aeonSolutions/AeonLabs-Solder-Reflow-Plate-PCB/Designs/photo1.jpg

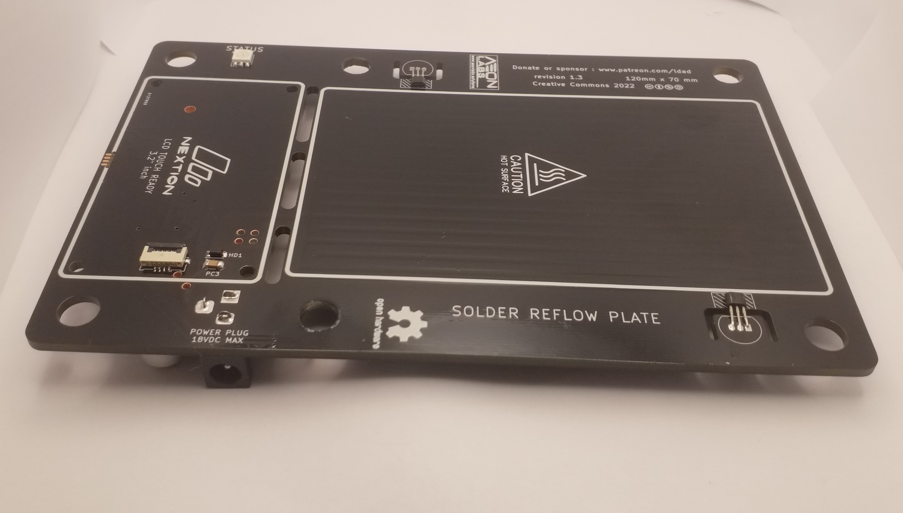
Designs/photo1.jpg
