aeonSolutions/AeonLabs-Solder-Reflow-Plate-PCB/Designs/photo2.jpg

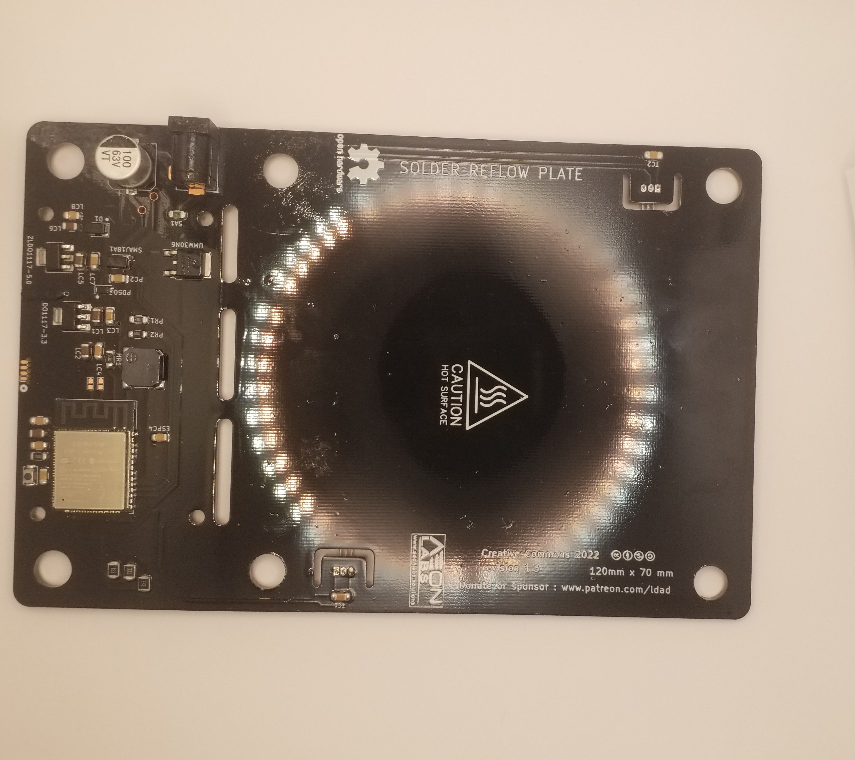
Designs/photo2.jpg
