aeonSolutions/AeonLabs-Solder-Reflow-Plate-PCB/Designs/photo3.jpg

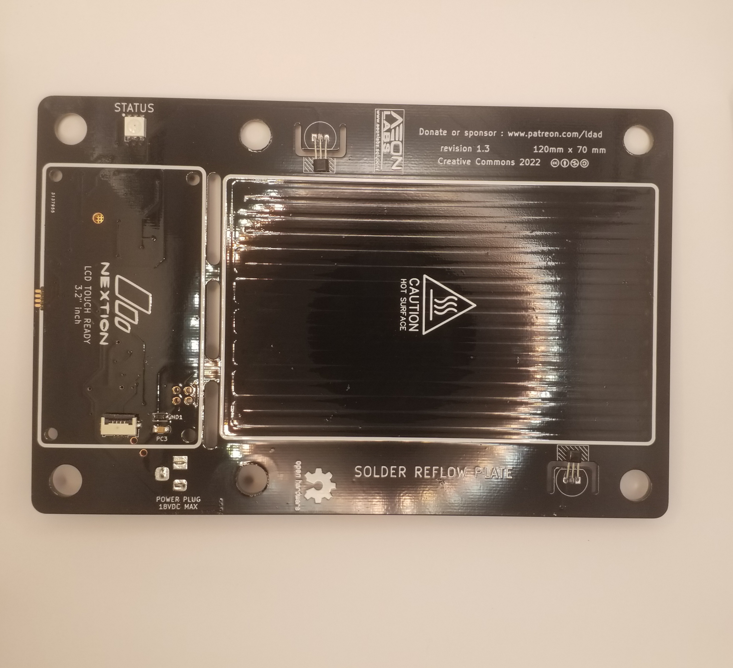
Designs/photo3.jpg
