aeonSolutions/AeonLabs-Solder-Reflow-Plate-PCB/Designs/photo4.jpg

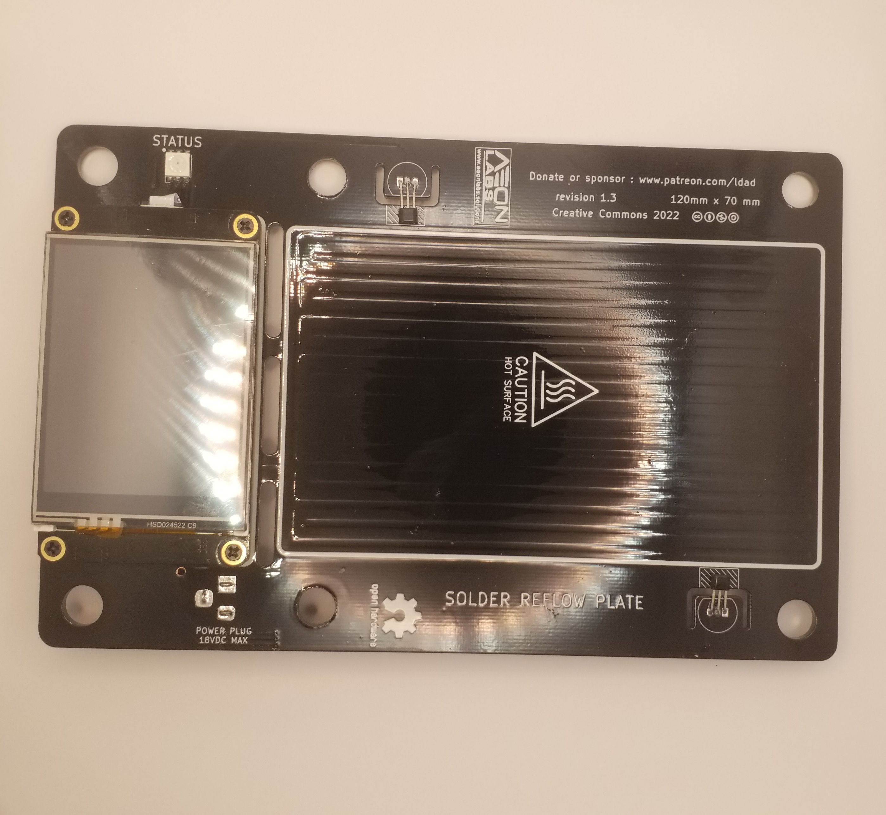
Designs/photo4.jpg
