aeonSolutions/AeonLabs-Solder-Reflow-Plate-PCB/Designs/photo5.jpg

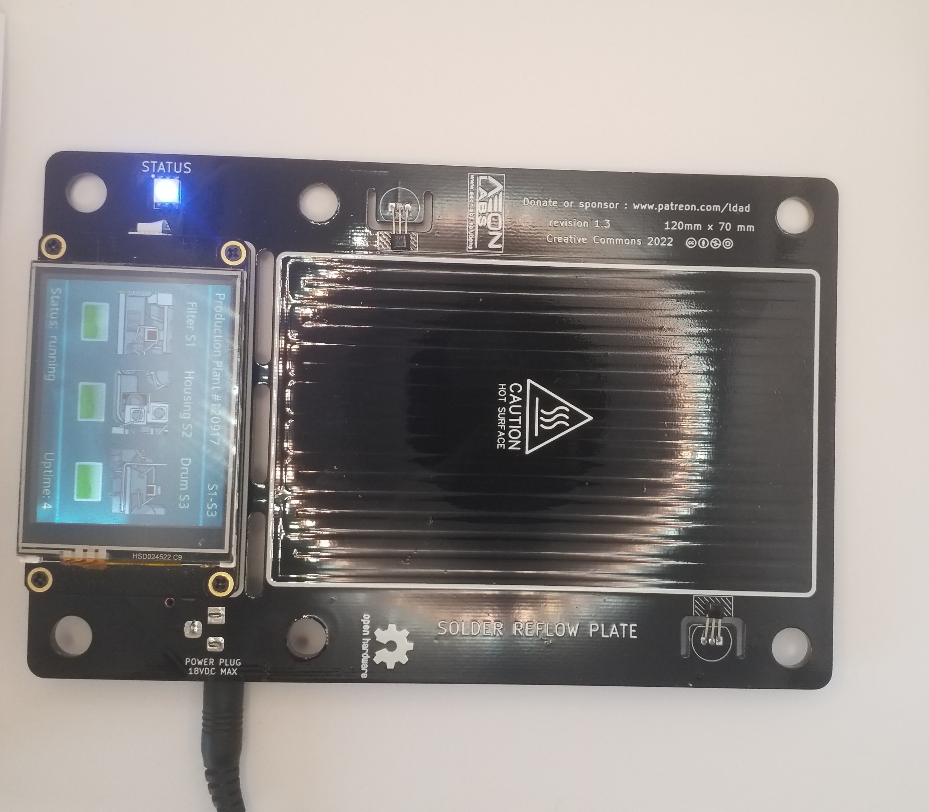
Designs/photo5.jpg
