aeonSolutions/AeonLabs-Solder-Reflow-Plate-PCB/Designs/photo6.jpg

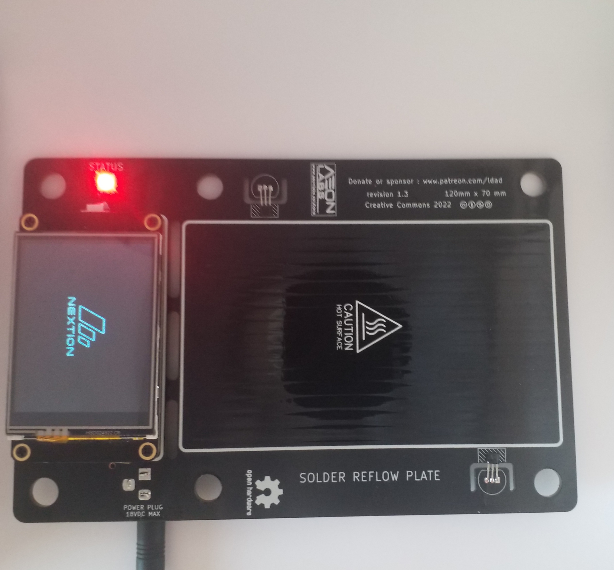
Designs/photo6.jpg
