aeonSolutions/AeonLabs-Solder-Reflow-Plate-PCB/Designs/photo7.jpg

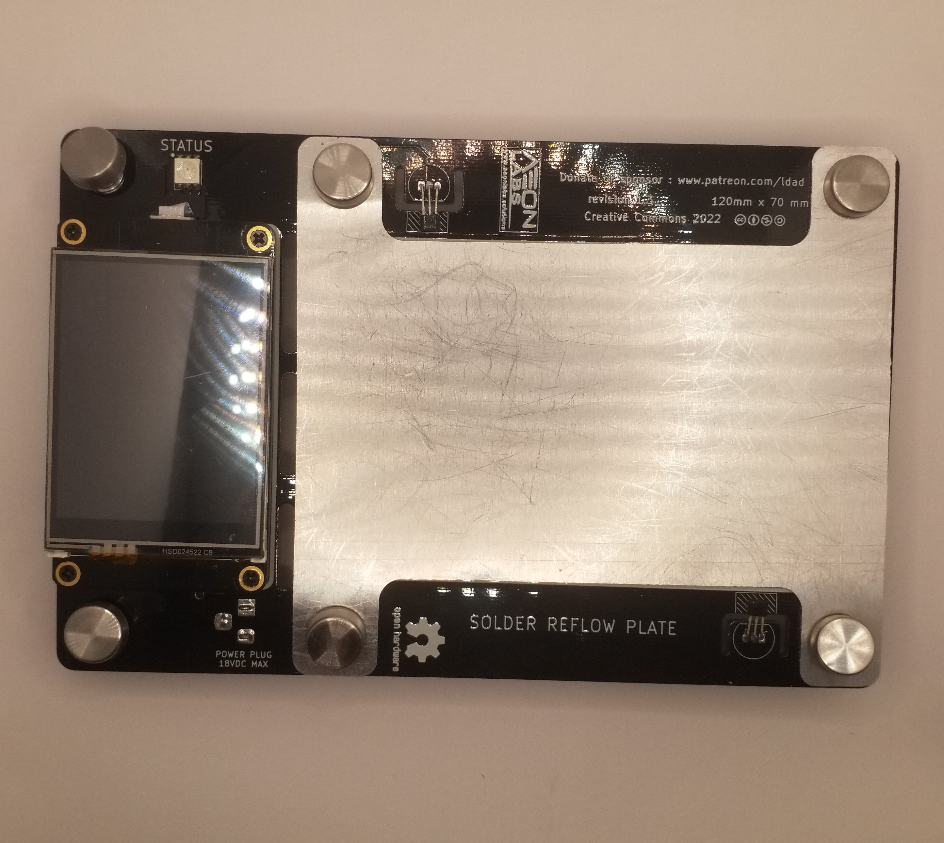
Designs/photo7.jpg
