aeonSolutions/AeonLabs-Solder-Reflow-Plate-PCB/Designs/photo8.jpg

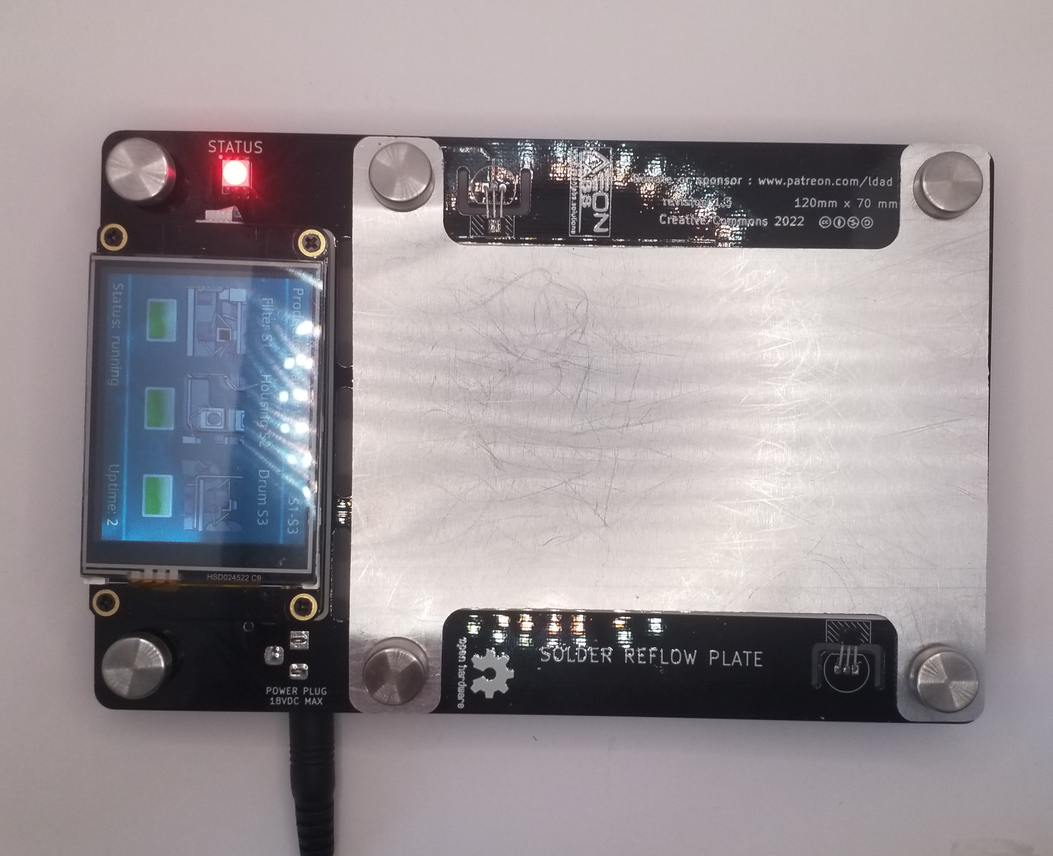
Designs/photo8.jpg
