aeonSolutions/AeonLabs-Solder-Reflow-Plate-PCB/Designs/photo9.jpg

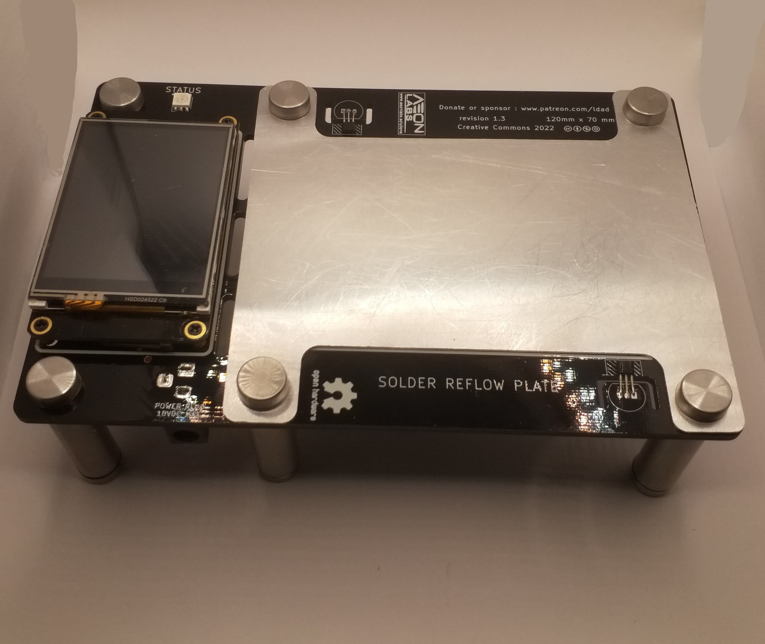
Designs/photo9.jpg
