aeonSolutions/AeonLabs-Solder-Reflow-Plate-PCB/Designs/photo10.jpg

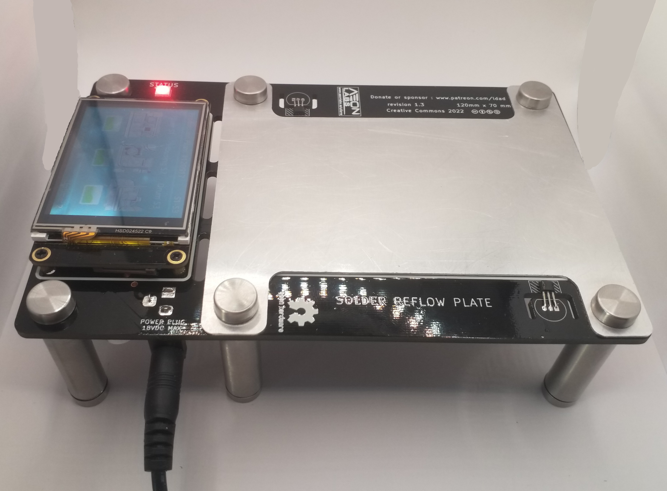
Designs/photo10.jpg
