aeonSolutions/AeonLabs-Solder-Reflow-Plate-PCB/Designs/photo11.jpg

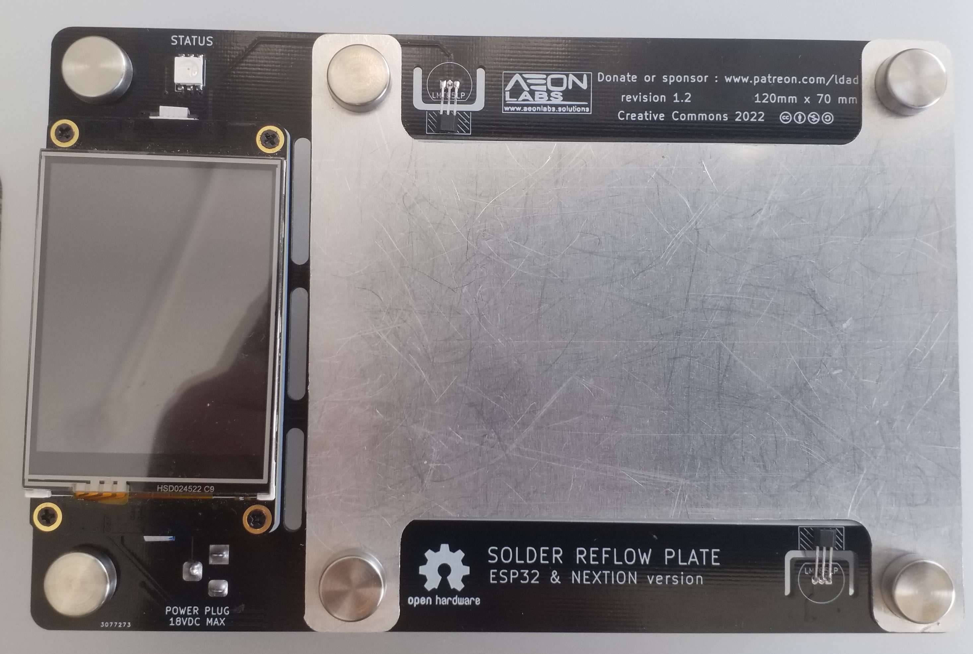
Designs/photo11.jpg
