aeonSolutions/AeonLabs-Solder-Reflow-Plate-PCB/Designs/photo12.jpg

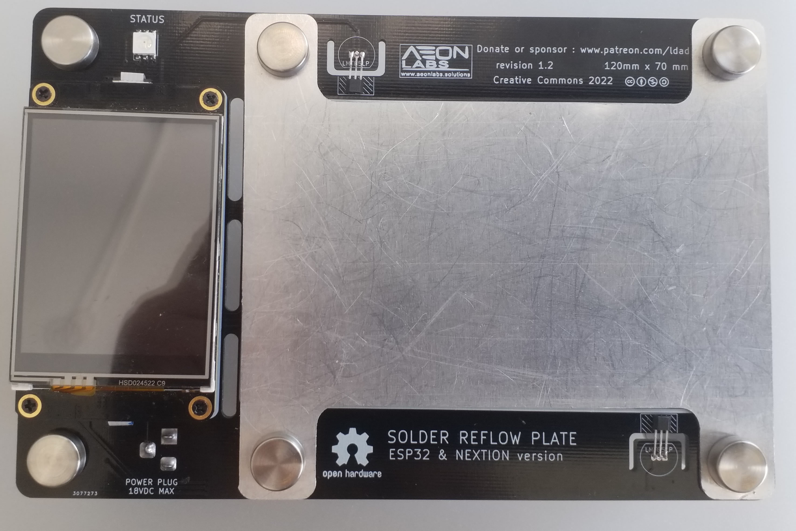
Designs/photo12.jpg
