aeonSolutions/AeonLabs-Solder-Reflow-Plate-PCB/Designs/photo13.jpg

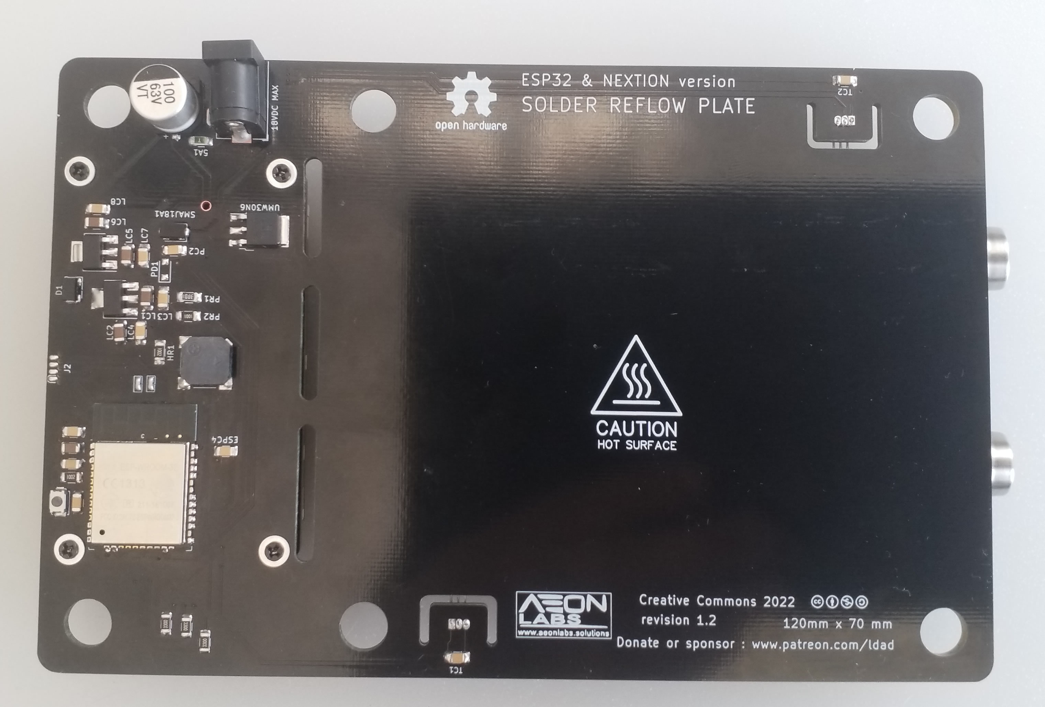
Designs/photo13.jpg
