aeonSolutions/AeonLabs-Solder-Reflow-Plate-PCB/Designs/photo14.jpg

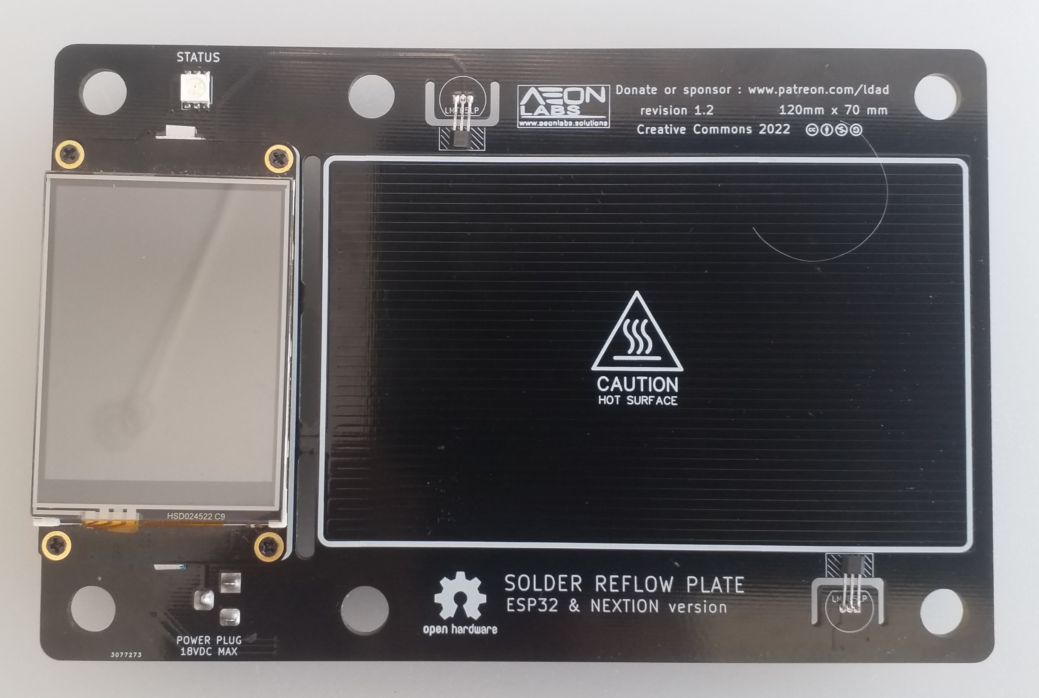
Designs/photo14.jpg
