aeonSolutions/AeonLabs-Solder-Reflow-Plate-PCB/ESP32 NEXTION/Nextion/graphics/welcome_backG.fw.png

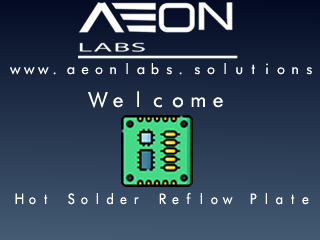
ESP32 NEXTION/Nextion/graphics/welcome_backG.fw.png
