aeonSolutions/AeonLabs-Solder-Reflow-Plate-PCB/ESP32 NEXTION/Arduino Studio/Blink_aeon/Tone32.h

#ifndef _TONE32_h
#define _TONE32_h

#define TONE_CHANNEL 15
#include "Arduino.h"
#include "pitches.h"

void tone32(uint8_t pin, unsigned int frequency, unsigned long duration = 0, uint8_t channel = TONE_CHANNEL);
void noTone32(uint8_t pin, uint8_t channel = TONE_CHANNEL);
#endif
